coloradoprintingproject/microcluster/cad/side_panel_24x36in.fcstd

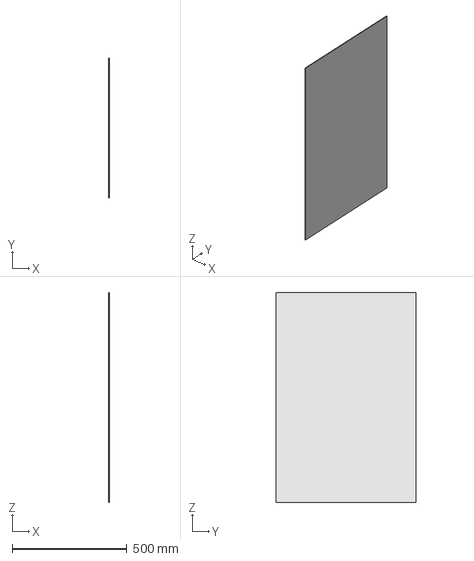
[picture p19: CAD file, 2018-04-23]
cad/side_panel_24x36in.fcstd
3.18 x 609.6 x 914.4 mm
