coloradoprintingproject/microcluster/cad/shelf_corner.fcstd

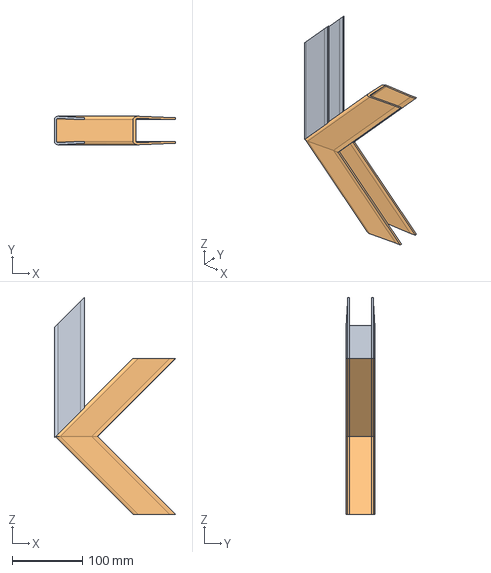
[picture p20: CAD file, 2018-04-23]
cad/shelf_corner.fcstd
172.7 x 40.8 x 309.0 mm
