coloradoprintingproject/microcluster/cad/slider-guider.fcstd

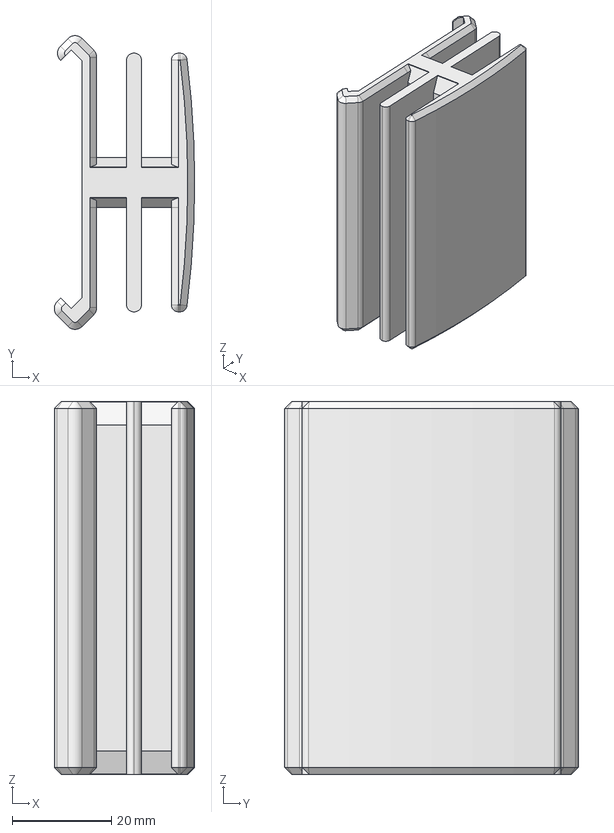
[picture p21: CAD file, 2018-04-23]
cad/slider-guider.fcstd
28.2 x 59.1 x 75.0 mm
