coloradoprintingproject/microcluster/cad/horizontal_support_48in.fcstd

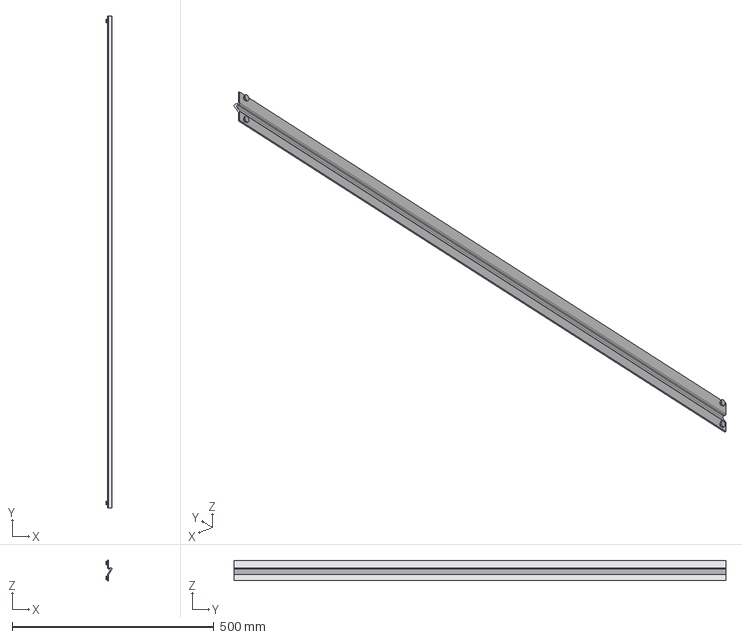
[picture p22: CAD file, 2018-04-23]
cad/horizontal_support_48in.fcstd
15.5 x 1219.2 x 50.8 mm
