coloradoprintingproject/microcluster/cad/LED-remote-bezel-inside.fcstd

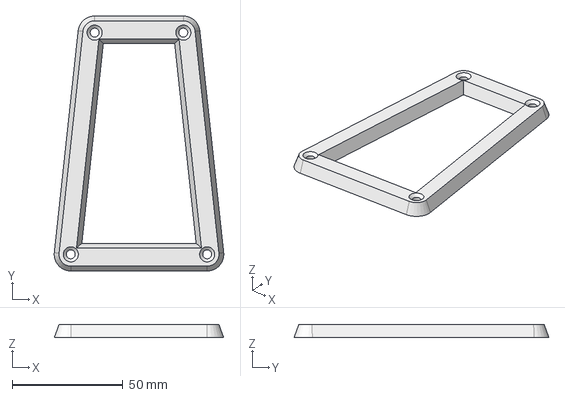
[picture p23: CAD file, 2018-04-23]
cad/LED-remote-bezel-inside.fcstd
76.5 x 115.0 x 6.00 mm
